arkadiraf/Smart_Juggling_Balls/Chess_Timer/Images/20150825_155303.jpg

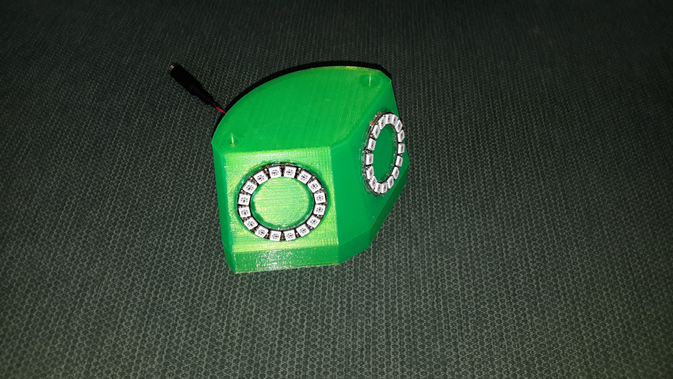
Chess_Timer/Images/20150825_155303.jpg
