arkadiraf/Smart_Juggling_Balls/Chess_Timer/Images/20150825_155438.jpg

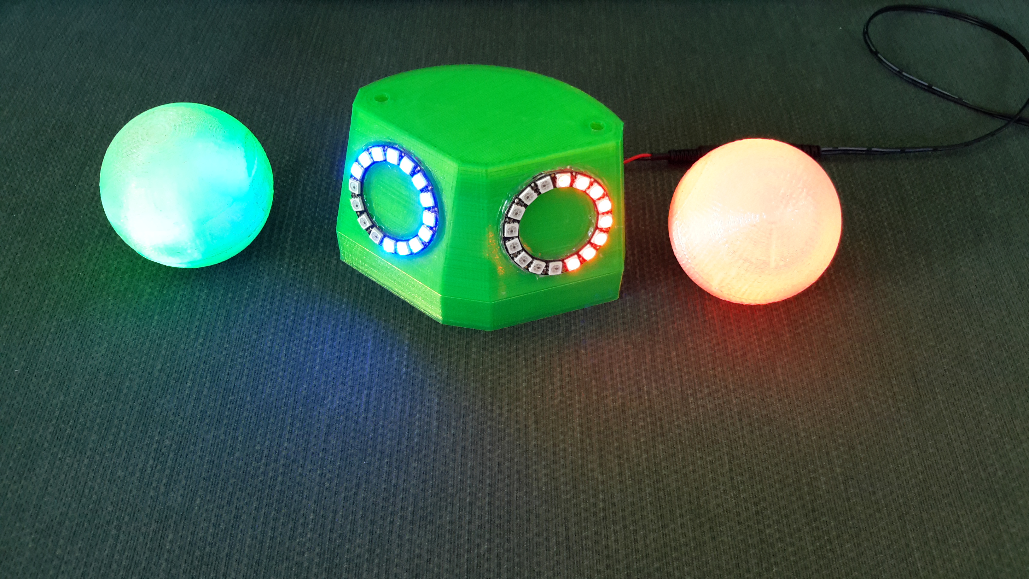
Chess_Timer/Images/20150825_155438.jpg
