arkadiraf/Smart_Juggling_Balls/Chess_Timer/Images/20150906_152935.jpg

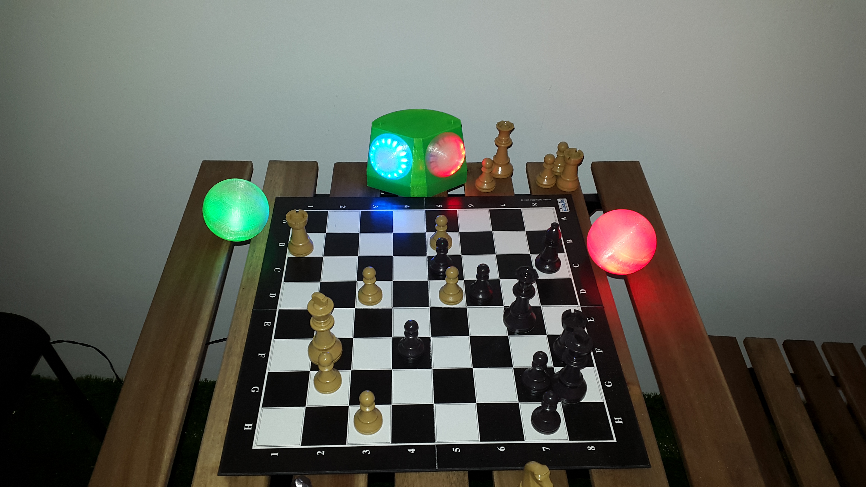
Chess_Timer/Images/20150906_152935.jpg
