arkadiraf/Smart_Juggling_Balls/Images/Centrifugal force.gif

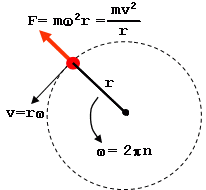
Images/Centrifugal force.gif
