arkadiraf/Smart_Juggling_Balls/ShakeIt/Images/20150505_113751.jpg

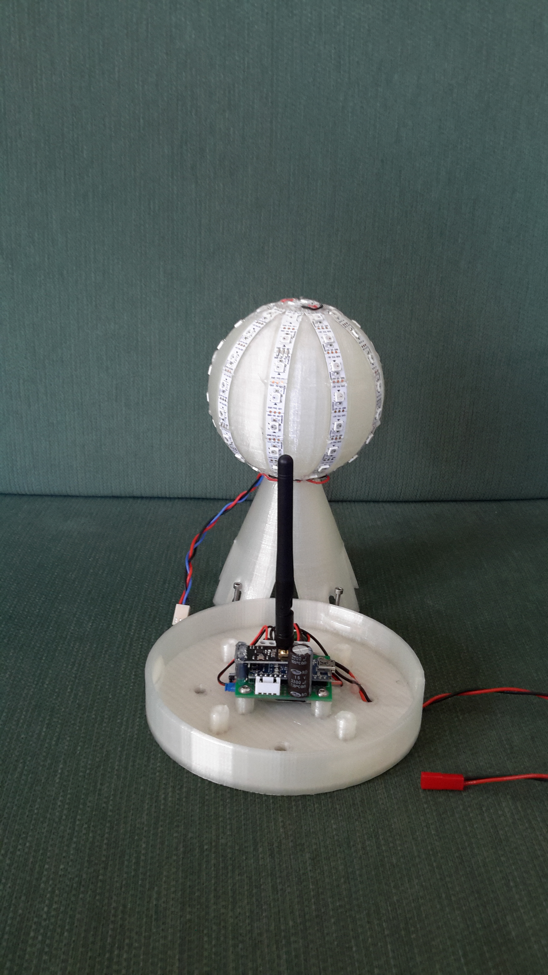
ShakeIt/Images/20150505_113751.jpg
