arkadiraf/Smart_Juggling_Balls/ShakeIt/Images/20150505_113824.jpg

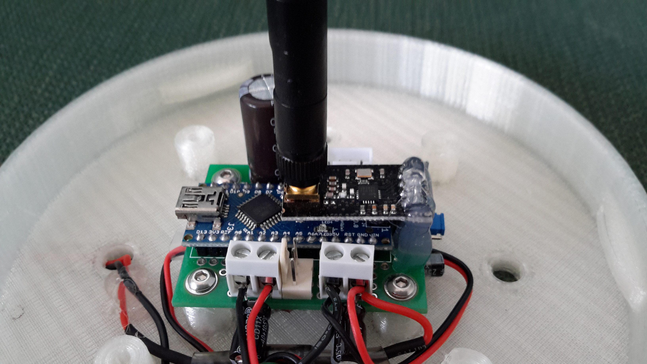
ShakeIt/Images/20150505_113824.jpg
