arkadiraf/Smart_Juggling_Balls/ShakeIt/Images/Game_Mode.jpg

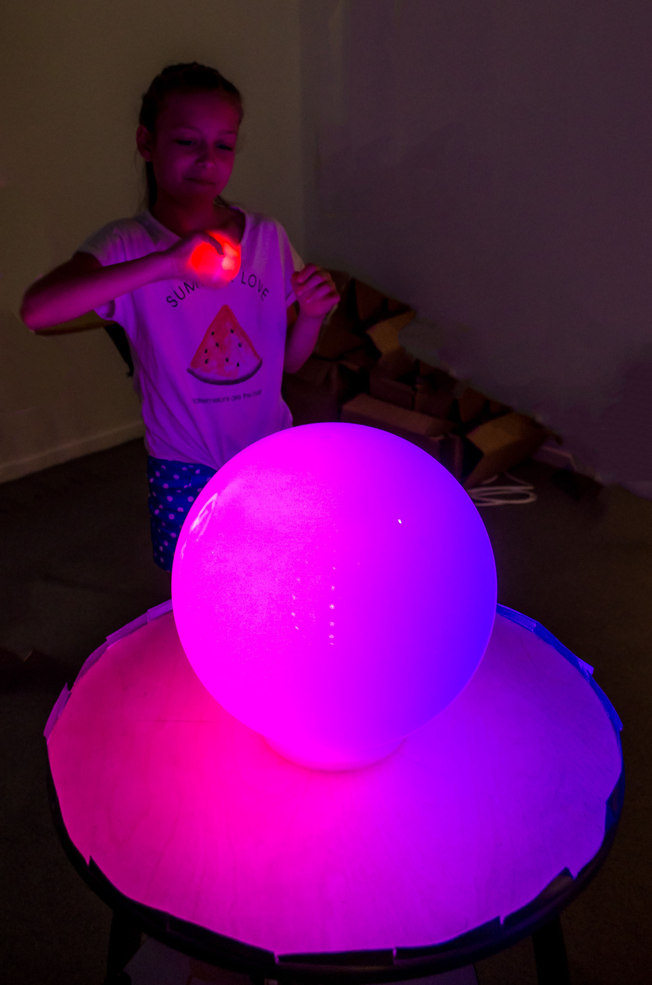
ShakeIt/Images/Game_Mode.jpg
